inestvan/sprut.korpus/docs/monitor/displayA_front_size.png

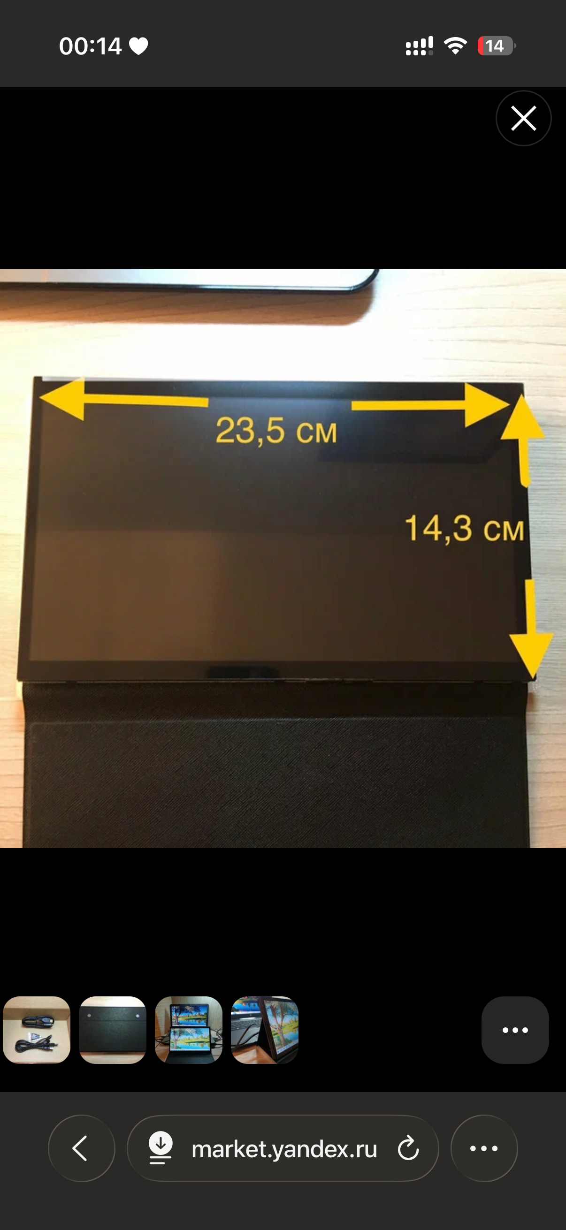
docs/monitor/displayA_front_size.png
