inestvan/sprut.korpus/docs/monitor/other_variant/jrp1133_accessories.jpg

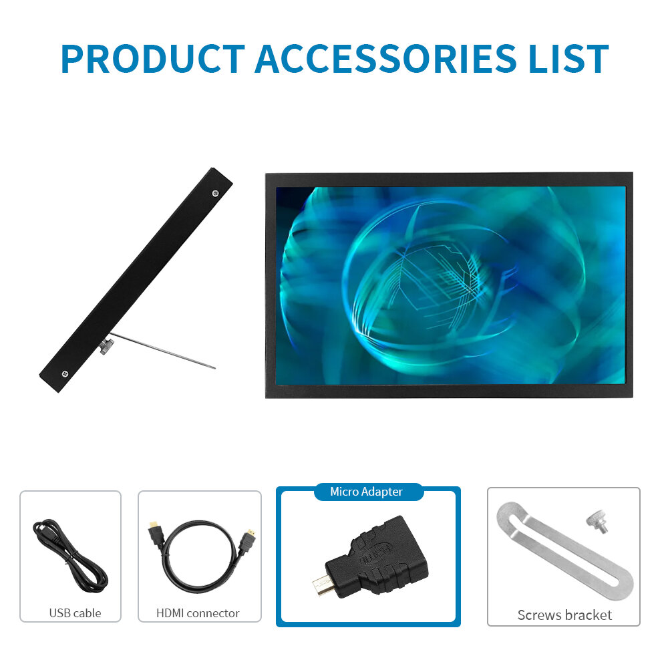
docs/monitor/other_variant/jrp1133_accessories.jpg
