inestvan/sprut.korpus/preview/box_bottom_wall.png

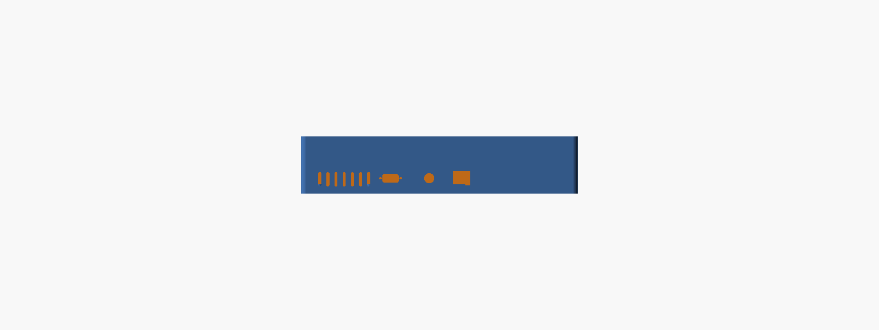
preview/box_bottom_wall.png
