inestvan/sprut.korpus/preview/box_iso.png

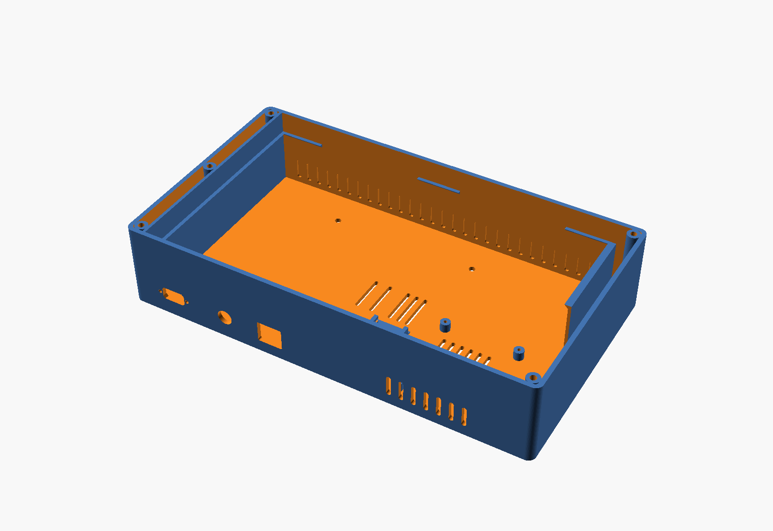
preview/box_iso.png
