inestvan/sprut.korpus/preview/edge_detail.png

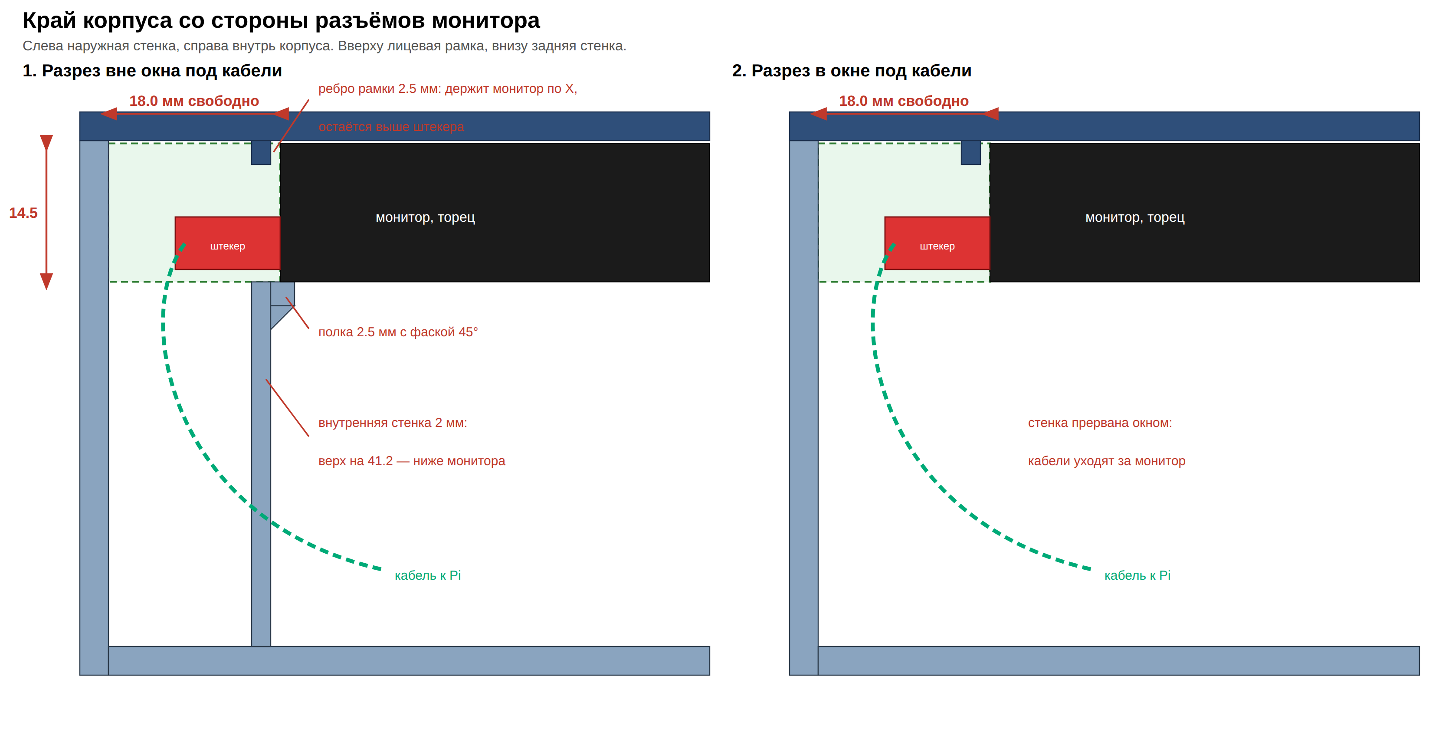
preview/edge_detail.png
