inestvan/sprut.korpus/preview/holders.png

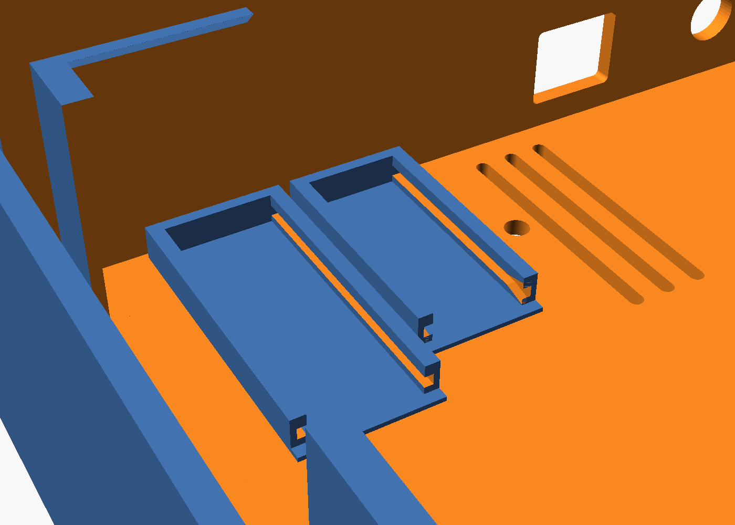
preview/holders.png
