inestvan/sprut.korpus/preview/layout_top.png

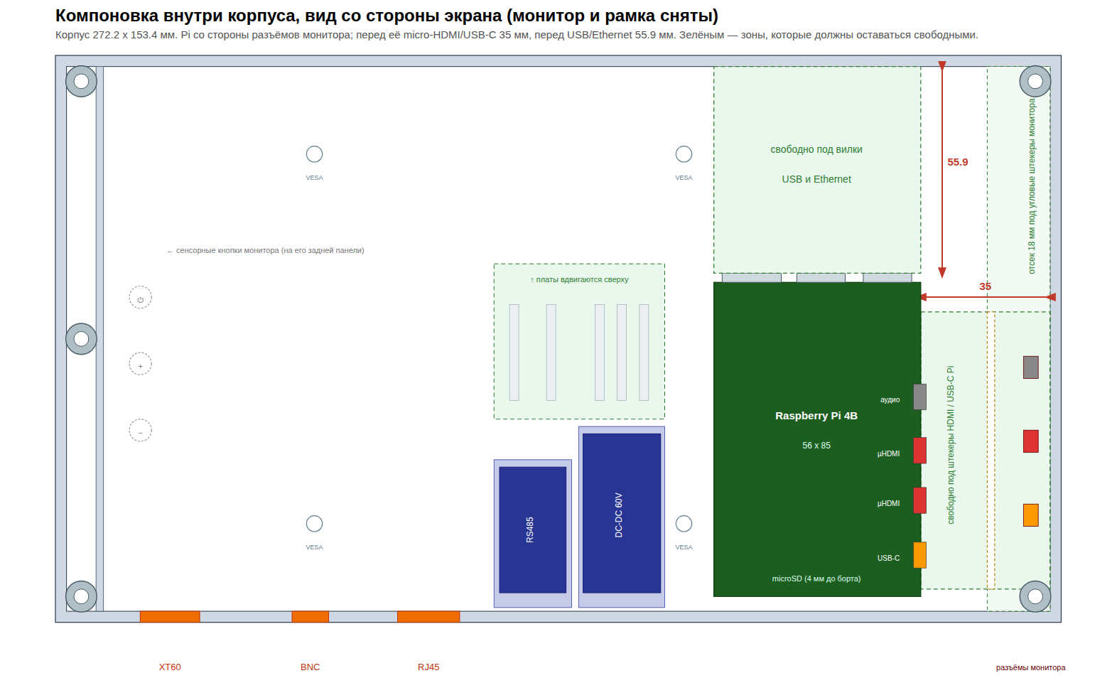
preview/layout_top.png
