inestvan/sprut.korpus/preview/scheme_placement.png

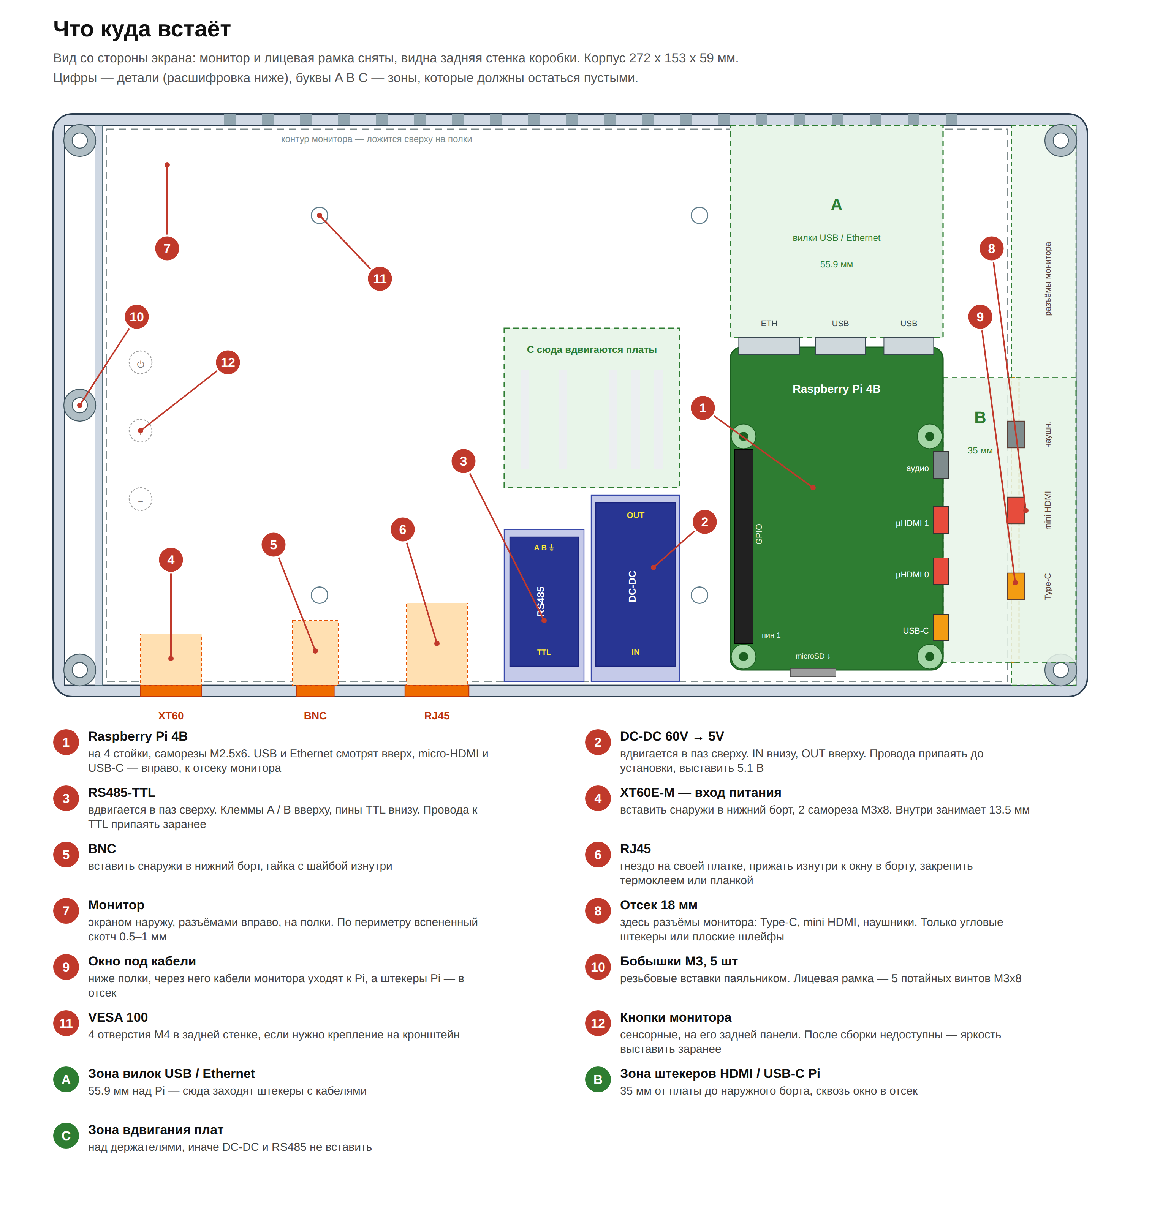
preview/scheme_placement.png
