inestvan/sprut.korpus/preview/section_conn.png

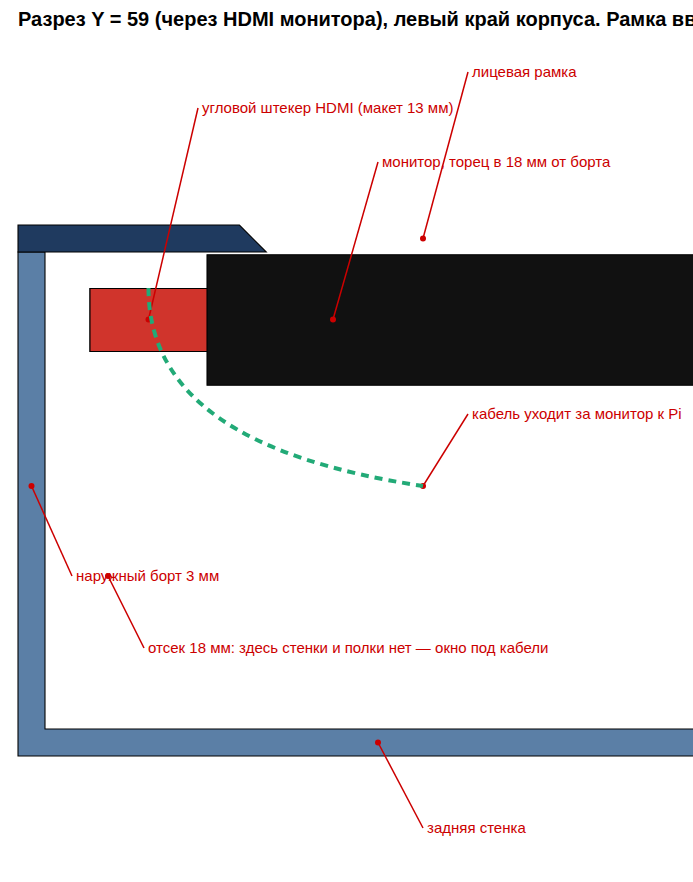
preview/section_conn.png
