inestvan/sprut.korpus/preview/section_x.png

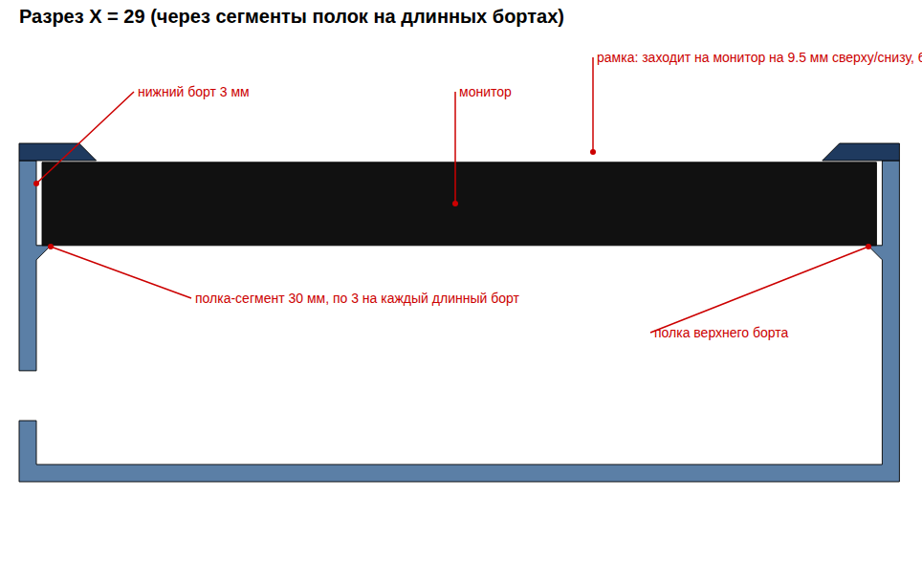
preview/section_x.png
