inestvan/sprut.korpus/preview/section_y.png

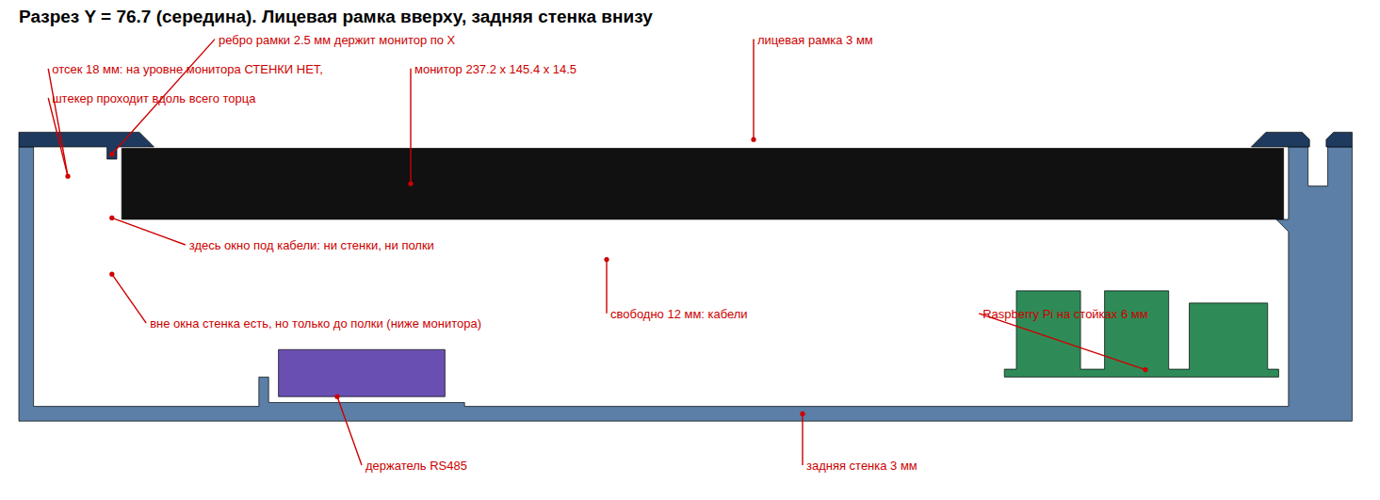
preview/section_y.png
