inestvan/sprut.korpus/preview/assembly_front.png

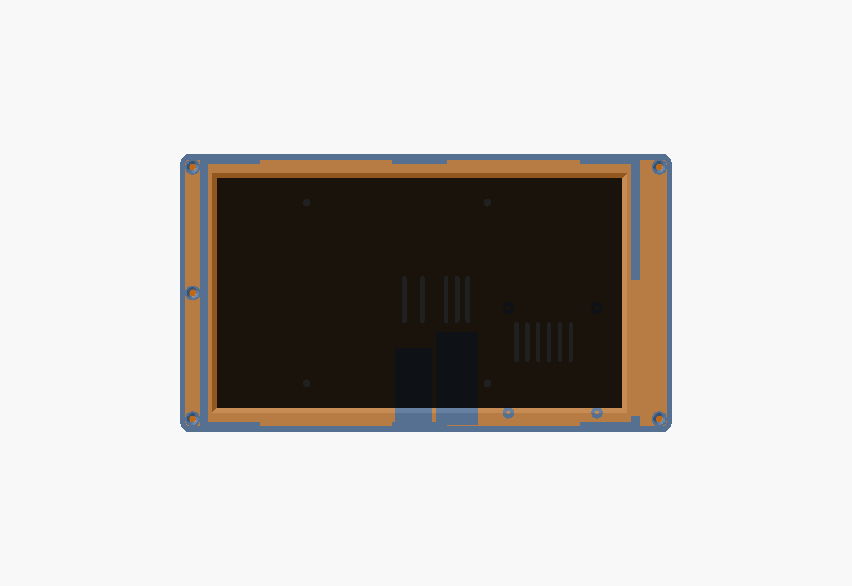
preview/assembly_front.png
