inestvan/sprut.korpus/preview/assembly_iso.png

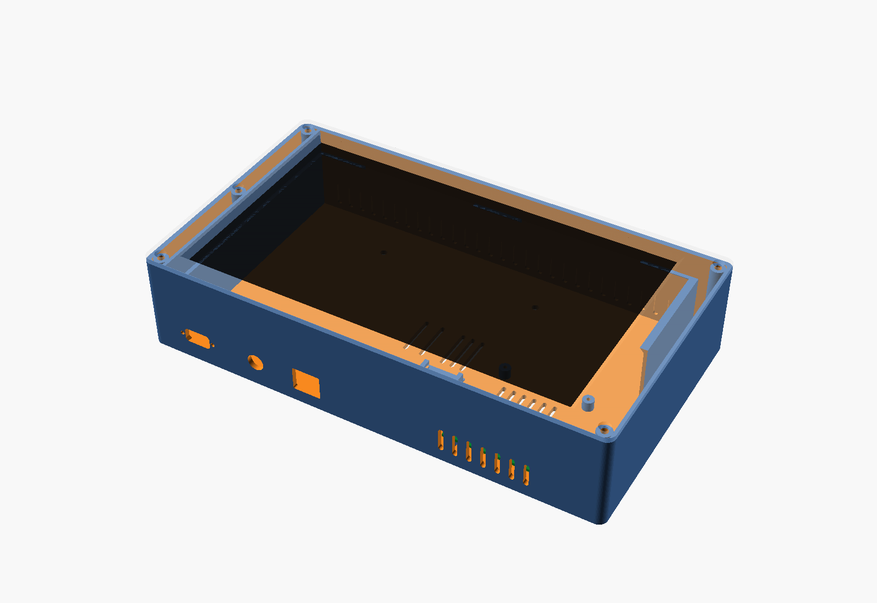
preview/assembly_iso.png
