inestvan/sprut.korpus/preview/bezel_print.png

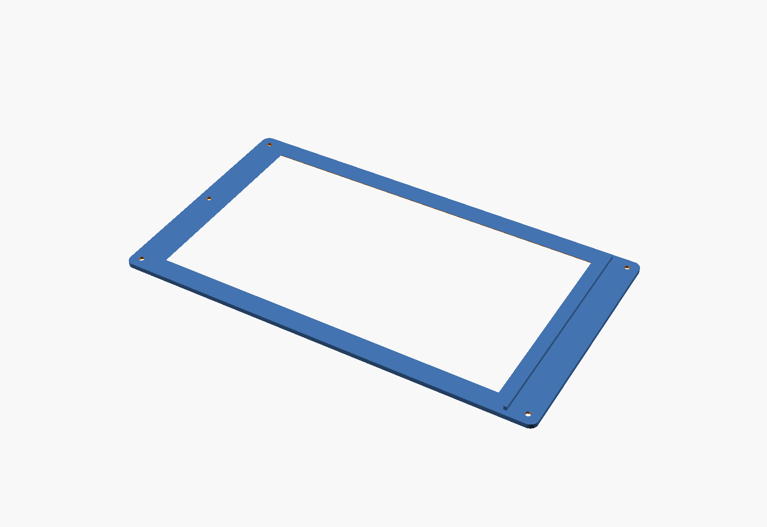
preview/bezel_print.png
