inestvan/sprut.korpus/preview/scheme_wiring.png

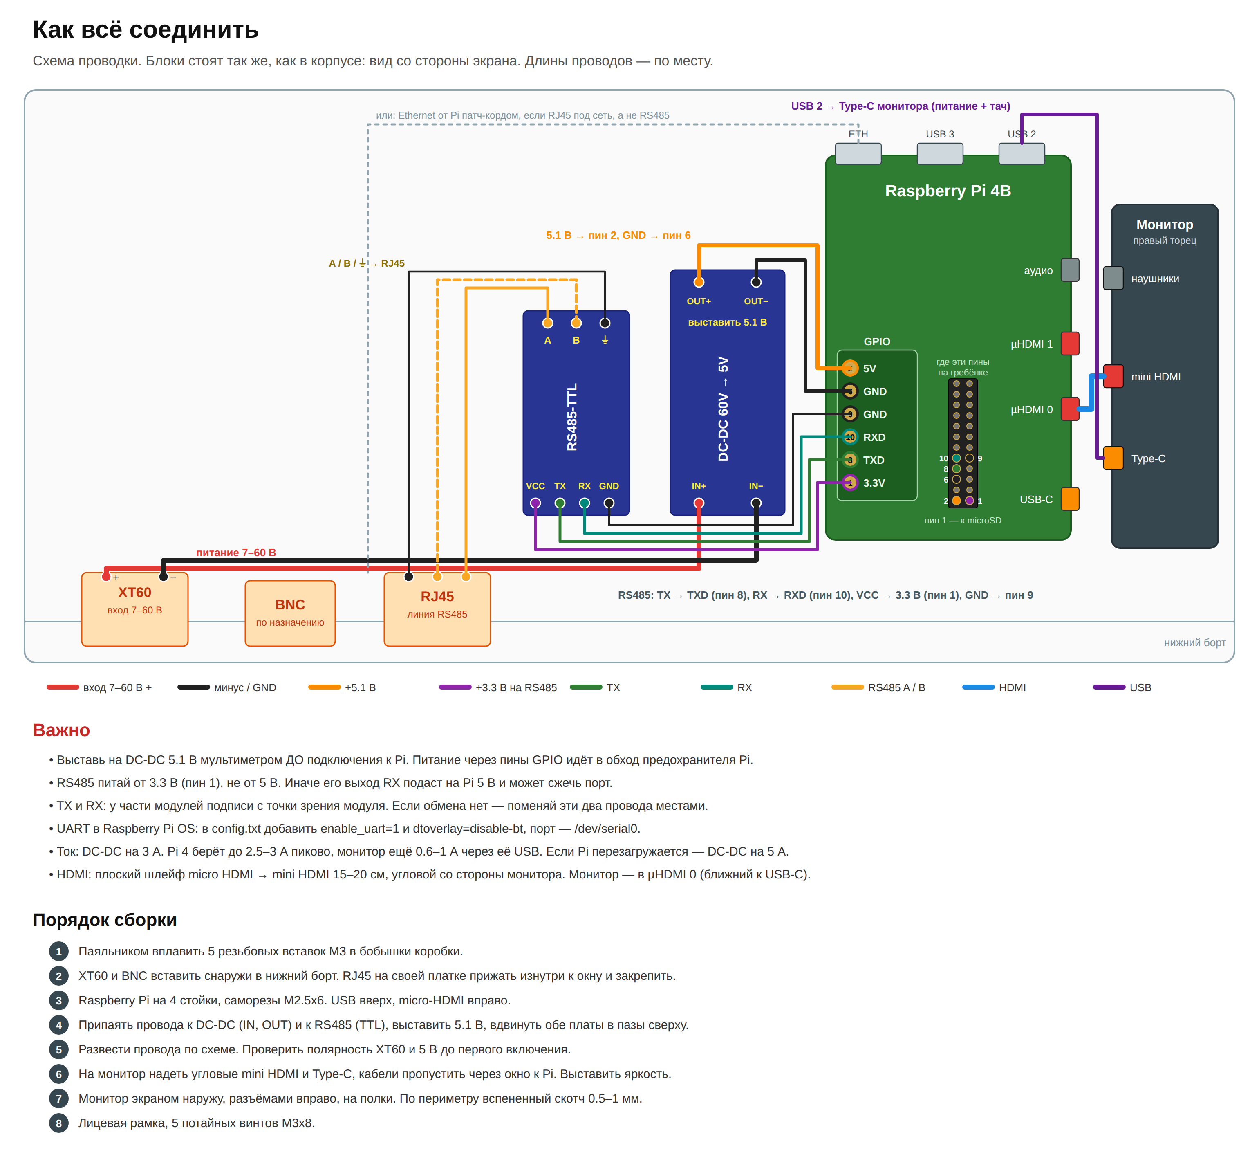
preview/scheme_wiring.png
